nicnic-cc/trmnl-mini/docs/IMG_8576.jpeg

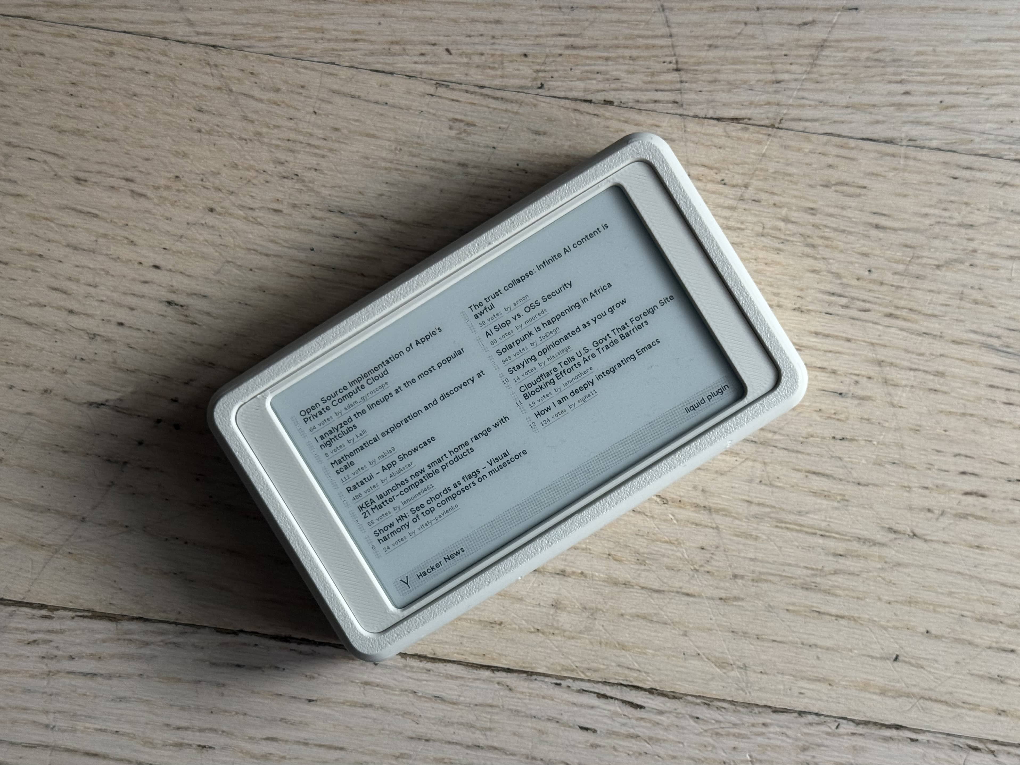
docs/IMG_8576.jpeg
